Matheus2201645/SistemaIrrigacao/STLs/baseVasoV2.STL

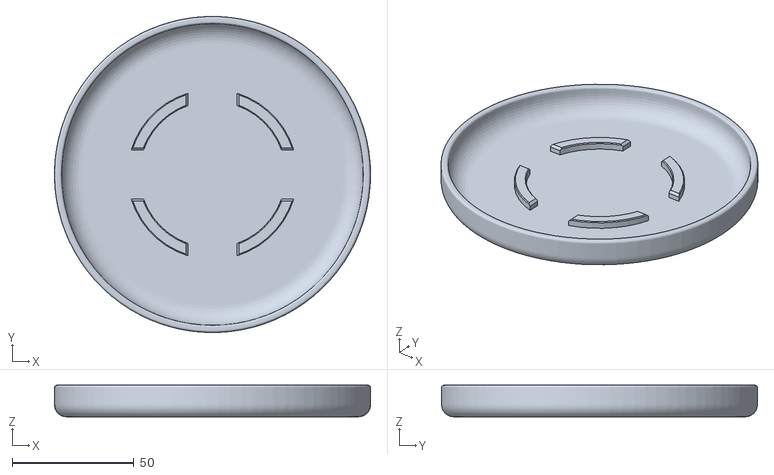
[picture p47: CAD file, 2025-06-27]
STLs/baseVasoV2.STL
130.0 x 130.0 x 13.0
