Matheus2201645/SistemaIrrigacao/STLs/ChassiValvula.STL

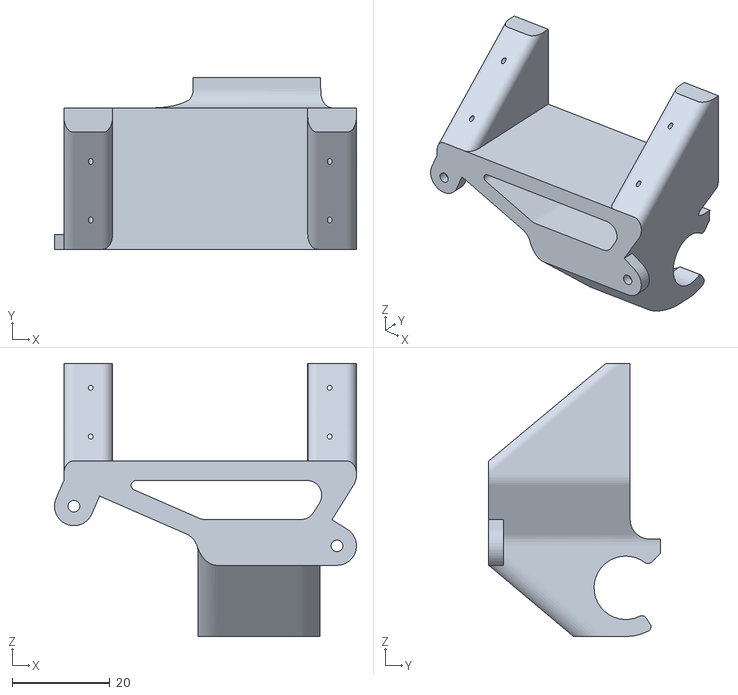
[picture p48: CAD file, 2025-06-27]
STLs/ChassiValvula.STL
61.9 x 35.2 x 56.0
