Matheus2201645/SistemaIrrigacao/STLs/SuporteSensor.STL

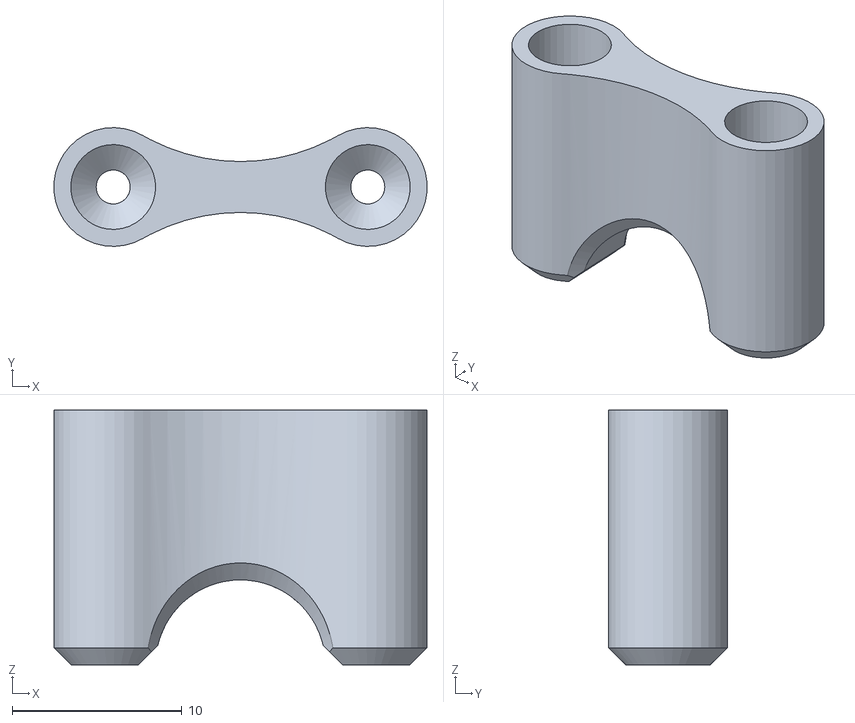
[picture p49: CAD file, 2025-06-27]
STLs/SuporteSensor.STL
22.0 x 7.00 x 15.0
