Matheus2201645/SistemaIrrigacao/STLs/engrenagemValvula.STL

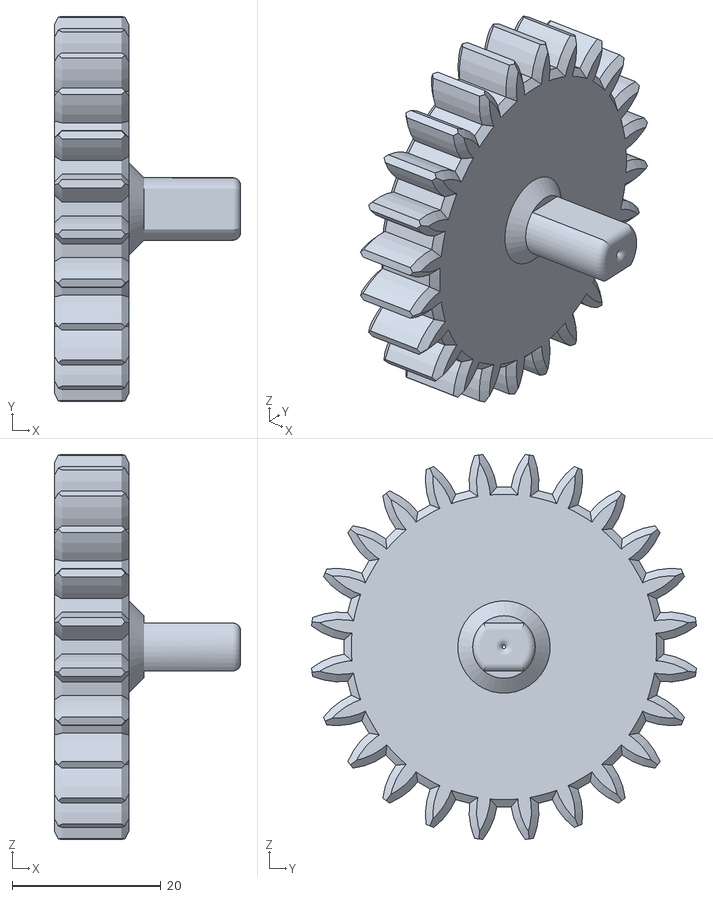
[picture p50: CAD file, 2025-06-27]
STLs/engrenagemValvula.STL
25.0 x 51.7 x 51.7
